francesco-scar/Elaborato-2021/Draws/3D_render.png

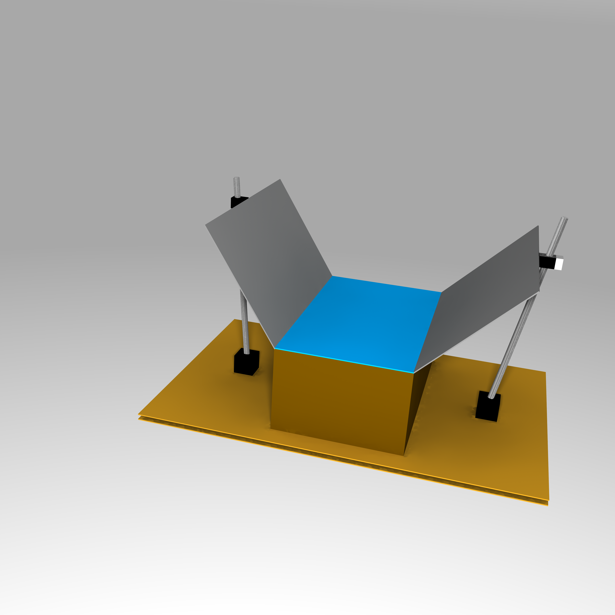
Draws/3D_render.png
