francesco-scar/Elaborato-2021/Draws/ADNS-2610_die/WIN_20210501_17_49_54_Pro.jpg

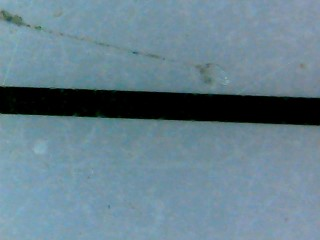
Draws/ADNS-2610_die/WIN_20210501_17_49_54_Pro.jpg
