francesco-scar/Elaborato-2021/Draws/ADNS-2610_die/WIN_20210501_18_11_32_Pro.jpg

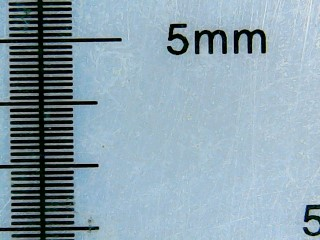
Draws/ADNS-2610_die/WIN_20210501_18_11_32_Pro.jpg
