francesco-scar/Elaborato-2021/Draws/default_image_sun_matrix.png

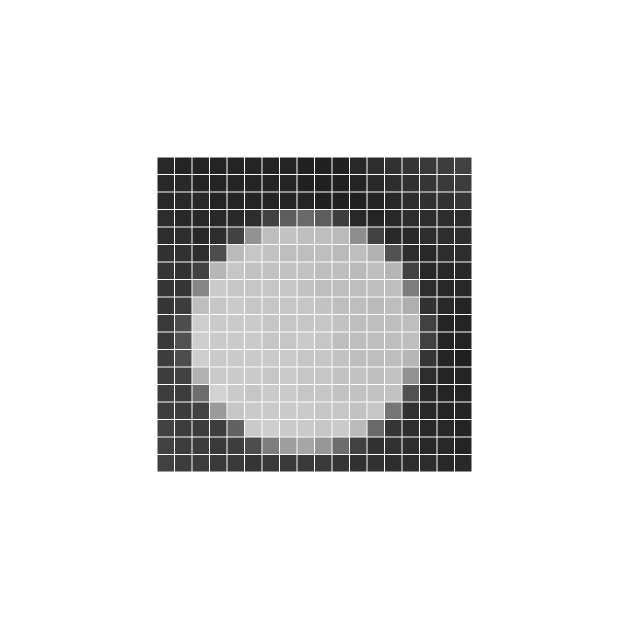
Draws/default_image_sun_matrix.png
