francesco-scar/Elaborato-2021/Draws/matplotlib_draws/2d_descent_1.png

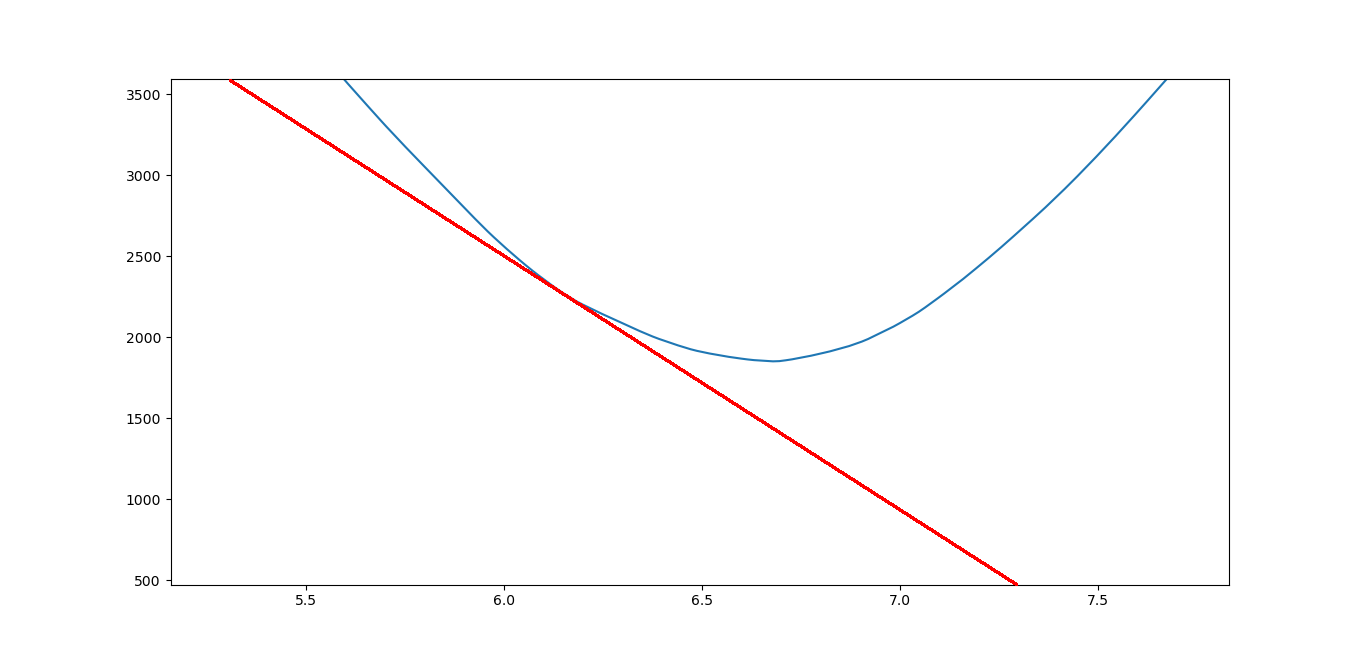
Draws/matplotlib_draws/2d_descent_1.png
