francesco-scar/Elaborato-2021/Draws/matplotlib_draws/2d_descent_2.png

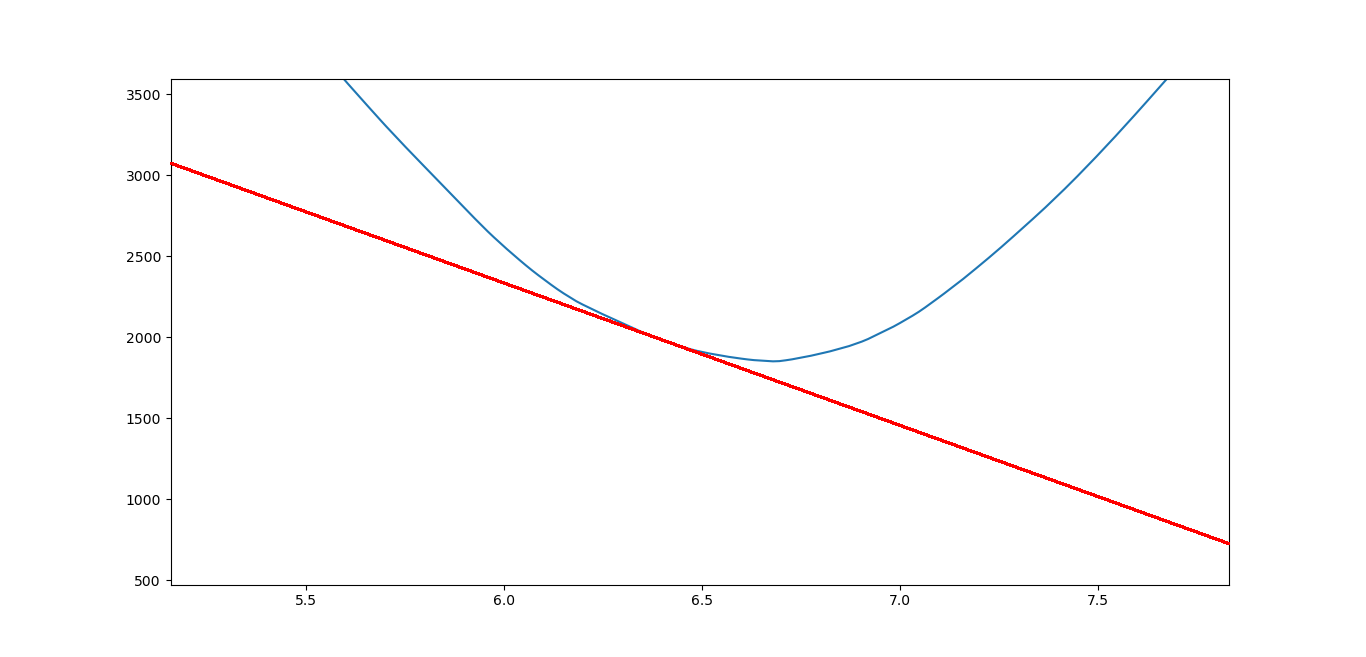
Draws/matplotlib_draws/2d_descent_2.png
