francesco-scar/Elaborato-2021/Draws/matplotlib_draws/3d_descent_base.png

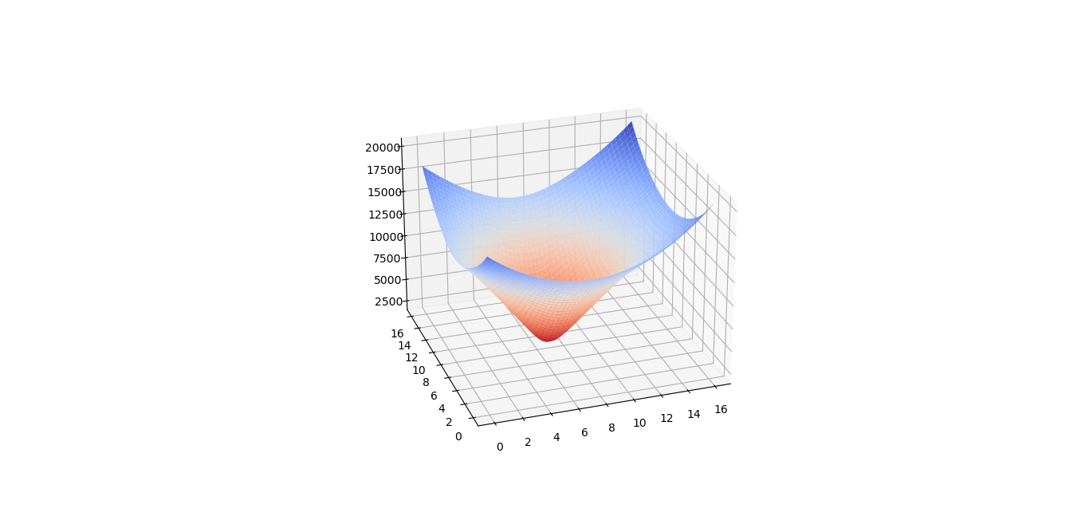
Draws/matplotlib_draws/3d_descent_base.png
