francesco-scar/Elaborato-2021/Draws/matplotlib_draws/3d_double_min.png

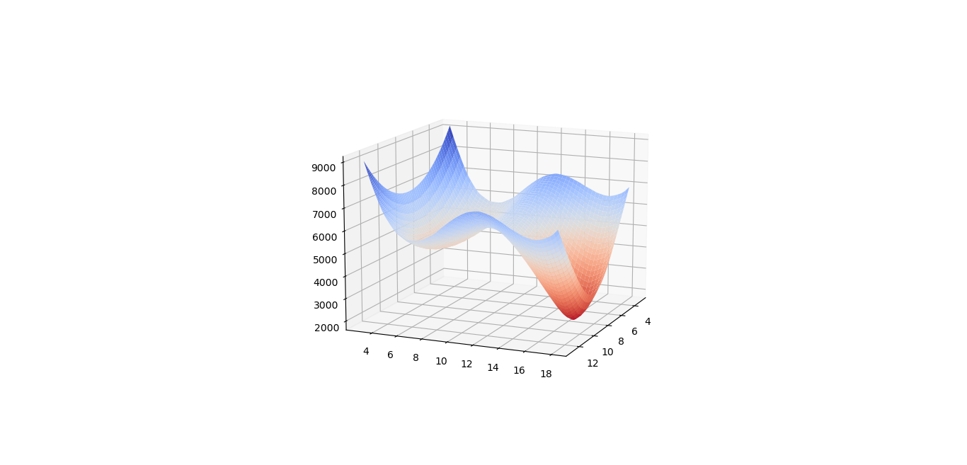
Draws/matplotlib_draws/3d_double_min.png
