francesco-scar/Elaborato-2021/Draws/matplotlib_draws/4d_descent_volume_fill.png

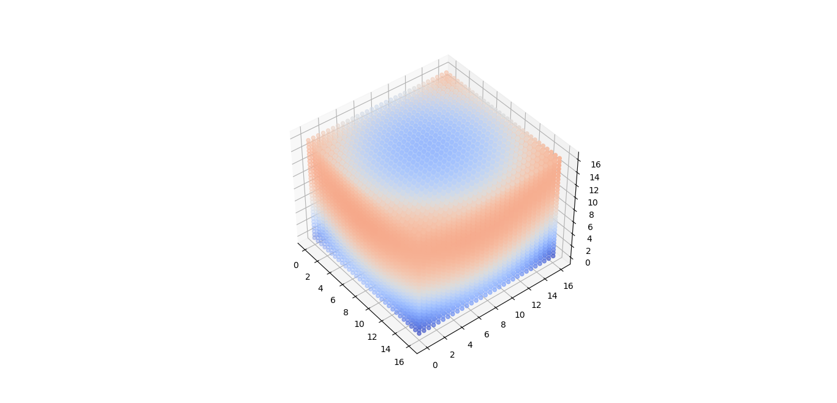
Draws/matplotlib_draws/4d_descent_volume_fill.png
