francesco-scar/Elaborato-2021/Draws/matplotlib_draws/double_min_canvas_border.png

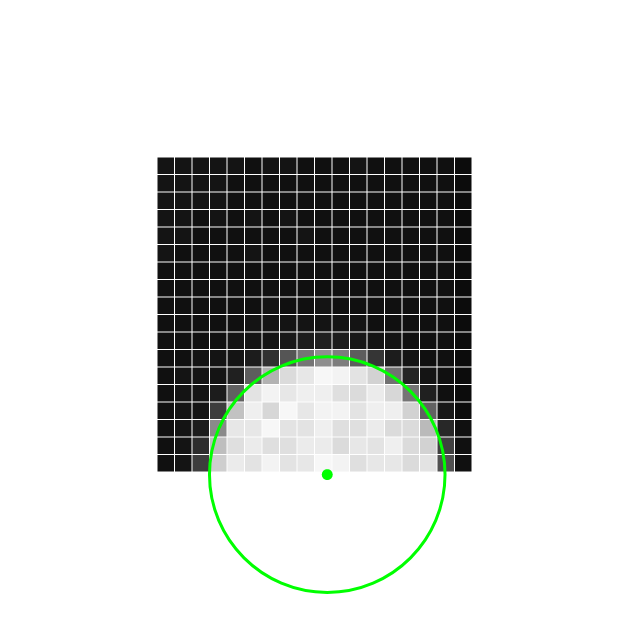
Draws/matplotlib_draws/double_min_canvas_border.png
