francesco-scar/Elaborato-2021/Draws/Motors_a.png

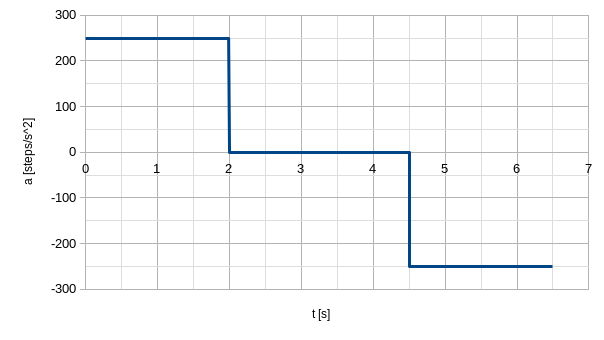
Draws/Motors_a.png
