francesco-scar/Elaborato-2021/Draws/Motors_s-v-a_line.png

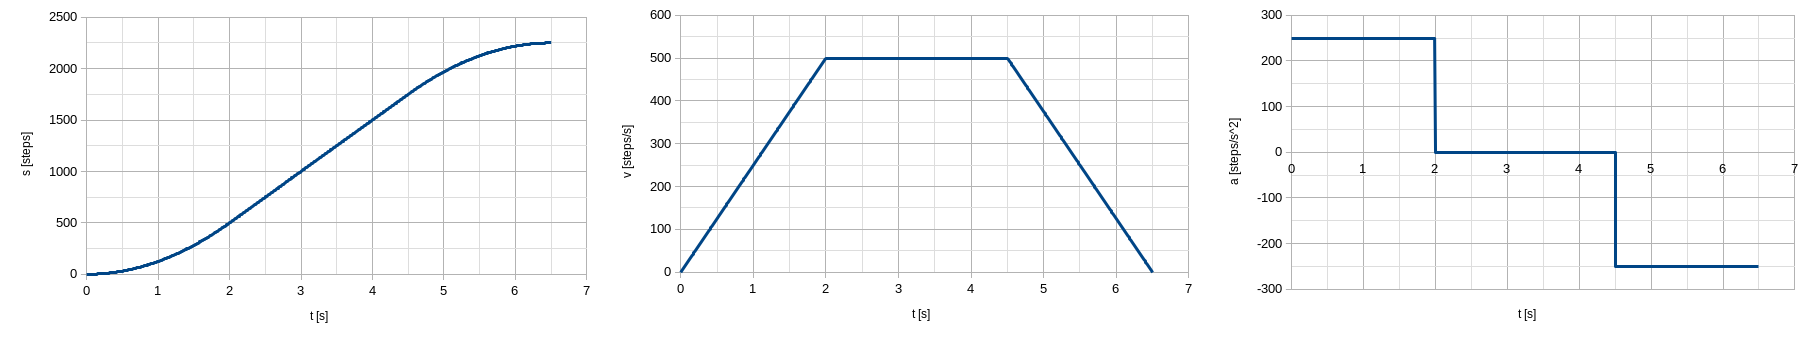
Draws/Motors_s-v-a_line.png
