francesco-scar/Elaborato-2021/Draws/Motors_s.png

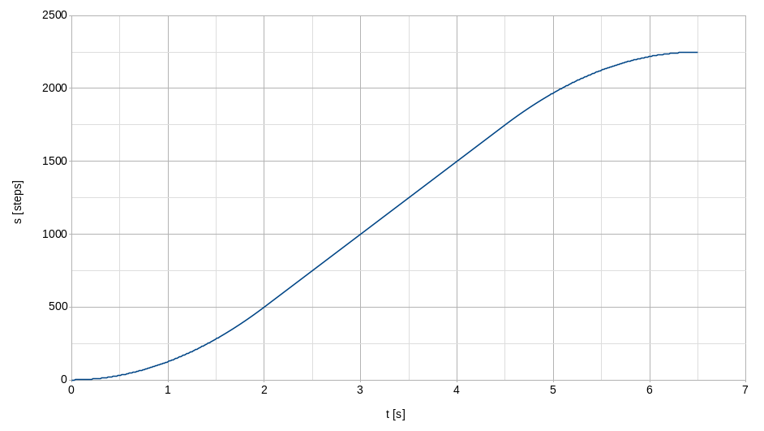
Draws/Motors_s.png
