francesco-scar/Elaborato-2021/Draws/Motors_v.png

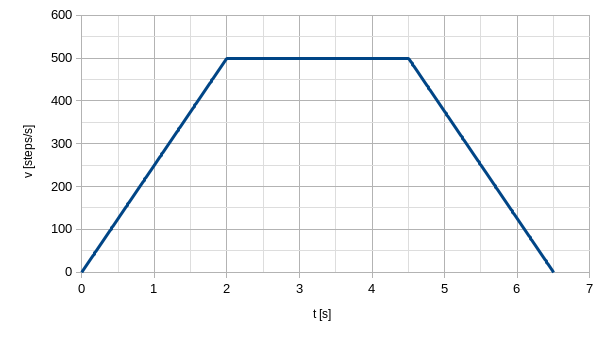
Draws/Motors_v.png
