francesco-scar/Elaborato-2021/Mouse_optical_sensor/ESP8266_web/sensor_functions.h

void getImageMatrix(uint8_t *matrix);
void print_full_bin(uint8_t bin);
void println_full_bin(uint8_t bin);
void write(uint8_t register_addr, uint8_t data);
uint8_t read(uint8_t register_addr);
void write_byte (uint8_t byte_val);
